pedalboard/pedalboard-case/parts/led-ring-rotary-washer.scad

include <lib/actuator.scad>

$fn = 50;
$vpr = [ 258.70, 0.00, 166.30 ];

led_ring_rotary_washer();
