pedalboard/pedalboard-case/parts/led-ring-washer.scad

include <lib/actuator.scad>

$fn=200;
$vpr=[ 258.70, 0.00, 166.30 ];

led_ring_washer();
